ohmic-net/puca_dsp/puca_dsp-platformio-arduino-esp32/original edition/arduino-esp32_stereo_chorus/src/controller_mod.h

/*!
 *  @file       effectmodule.h
 *  Project     Blackstomp Arduino Library
 *  @brief      Blackstomp Library for the Arduino
 *  @author     Hasan Murod
 *  @date       19/11/2020
 *  @license    MIT - Copyright (c) 2020 Hasan Murod
 *
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
 * THE SOFTWARE IS PROVIDED "AS IS", WITHOUT WARRANTY OF ANY KIND, EXPRESS OR
 * IMPLIED, INCLUDING BUT NOT LIMITED TO THE WARRANTIES OF MERCHANTABILITY,
 * FITNESS FOR A PARTICULAR PURPOSE AND NONINFRINGEMENT. IN NO EVENT SHALL THE
 * AUTHORS OR COPYRIGHT HOLDERS BE LIABLE FOR ANY CLAIM, DAMAGES OR OTHER
 * LIABILITY, WHETHER IN AN ACTION OF CONTRACT, TORT OR OTHERWISE, ARISING FROM,
 * OUT OF OR IN CONNECTION WITH THE SOFTWARE OR THE USE OR OTHER DEALINGS IN
 * THE SOFTWARE.
 */
#ifndef CONTROLLERMODULE_H_
#define CONTROLLERMODULE_H_

#include <Arduino.h>

typedef enum
{
  IM_LR,    //input mode = line-in L, line-in R
  IM_LMIC   //input mode = Line-in L, Microphone
} 
INPUT_MODE;

typedef enum
{
  EM_DISABLED,  //Not used
  EM_BUTTONS,   //Push buttons on encoder port
  EM_ROTARY     //Rotary encoder (with push button) on encoder port
} 
ENCODER_MODE;

typedef enum
{
  CM_DISABLED,  //not used
  CM_POT,       //potentiometer
  CM_SELECTOR,  //selector switch
  CM_TOGGLE,    //momentary push button as toggle switch
  CM_MOMENTARY, //momentary push button as momentary switch 
} 
CONTROL_MODE;

typedef enum
{
  BM_DISABLED,
  BM_MOMENTARY,
  BM_TOGGLE,
}
BUTTON_MODE;

struct BUTTON
{
  BUTTON_MODE mode;
  String name;
  bool inverted;
  bool touch;
  int min;
  int max;
  int value;
  int pin;
};

struct CONTROL
{
  String name;
  CONTROL_MODE mode;
  bool inverted;
  int min;
  int max;
  int levelCount;
  int value;
  bool slowSpeed;
  int pin;
};

struct BLETERMINAL
{
	String servUuid;
	String charUuid;
	uint32_t passKey;
};

class controllerModule
{
  public:
  String name;  //the name of your effect pedal
  INPUT_MODE inputMode; 
  ENCODER_MODE encoderMode;
  CONTROL control[6];
  BUTTON button[6];
  BLETERMINAL bleTerminal; 
  unsigned int runningTicks = 0;

  //base class constructor, do basic initialization, don't write a constructor in your descendant class
  controllerModule();
  //base desctructor, do basic deallocation, don't write a desttuctor in your descendant class
  ~controllerModule();

  //you have to write all initialization in the init() function of the  descendant class to set up
  //the name, inMode, and controls, memory allocation, and any other initialization
  virtual void init(){};

  //you have to write all deallocatoin in the deInit() function of the  descendant class for any deallocation
  virtual void deInit(){};

  //you have to overload the following event handler functions in your descendant class when its needed
  virtual void onControlChange(int controlIndex){};
  virtual void onButtonChange(int buttonIndex){};
  virtual void onButtonPress(int buttonIndex){};
  virtual void onButtonRelease(int buttonIndex){};
  virtual void onBleTerminalRequest(const char* request, char* response){};

};

#endif
