ohmic-net/puca_dsp/puca_dsp-platformio-arduino-esp32/original edition/arduino-esp32_stereo_chorus/src/bsdsp.cpp

/*!
 *  @file       bsdsp.cpp
 *  Project     Blackstomp Arduino Library
 *  @brief      Blackstomp Library for the Arduino
 *  @author     Hasan Murod
 *  @date       19/11/2020
 *  @license    MIT - Copyright (c) 2020 Hasan Murod
 *
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
 * THE SOFTWARE IS PROVIDED "AS IS", WITHOUT WARRANTY OF ANY KIND, EXPRESS OR
 * IMPLIED, INCLUDING BUT NOT LIMITED TO THE WARRANTIES OF MERCHANTABILITY,
 * FITNESS FOR A PARTICULAR PURPOSE AND NONINFRINGEMENT. IN NO EVENT SHALL THE
 * AUTHORS OR COPYRIGHT HOLDERS BE LIABLE FOR ANY CLAIM, DAMAGES OR OTHER
 * LIABILITY, WHETHER IN AN ACTION OF CONTRACT, TORT OR OTHERWISE, ARISING FROM,
 * OUT OF OR IN CONNECTION WITH THE SOFTWARE OR THE USE OR OTHER DEALINGS IN
 * THE SOFTWARE.
 */
  
#include "bsdsp.h"
#include "task.h"
#include <math.h>

//######################################################################
// LOOKUPLINEAR
float lookupLinear(float x, const float* table)
{
  int index = (int)x;
  float frac = x - (float)index;
  return table[index] + frac * (table[index+1]-table[index]);
}

//######################################################################
// SINE OSCILLATOR
#define MAXPHASE 255.0
oscillator::oscillator()
{
	phase = 0;
	phaseincrement = 0;
	setFrequency(20);
	waveTable = sin_table;
}

void oscillator::setWaveTable(const float* wtable)
{
	if(wtable==NULL)
		waveTable = sin_table;
	else waveTable = wtable;
}

void oscillator::update()
{
  phase = phase + phaseincrement;
  if(phase > MAXPHASE)
    phase = phase-MAXPHASE;
}

void oscillator::setPhase(float p)
{
	phase = p;
}

void oscillator::setFrequency(float freq)
{
  phaseincrement = freq * MAXPHASE /(float)SAMPLE_RATE;
}

float oscillator::getOutput(float phaseOffset)
{
  float p = phase + phaseOffset;
  if(p>MAXPHASE)
    p = p - MAXPHASE;
  return lookupLinear(p,waveTable);
}

float oscillator::getOutput()
{
  return lookupLinear(phase,waveTable);
}

//######################################################################
// BIQUAD FILTER
// Implementation of direct-form-2 biquad iir filter

//direct-form-2 biquad iir filter
struct biquadState
{
  float coef[5]; //a1, a2, b0, b1, b2
  float w[2];
};

biquadFilter::biquadFilter(int stageCount)
{
  stages = stageCount;
  biquadState* s = new biquadState[stages];
  states = (void*) s;
  for(int i=0;i<stages;i++)
  {
    s[i].w[0]=0;
    s[i].w[1]=0;
  }
}

/*
biquadFilter::~biquadFilter()
{
  biquadState* sp = (biquadState*) states;
  delete[] states;
}
*/

void biquadFilter::setCoef(const float* coef)
{
  biquadState* sp = (biquadState*) states;
  for(int i=0;i<stages;i++)
  {
    for(int n=0;n<5;n++)
      sp[i].coef[n]=coef[(5*i)+n];
  }
}

void biquadFilter::reset()
{
	biquadState* sp = (biquadState*) states;
    for(int i=0;i<stages;i++)
    {
      sp[i].w[0]=0;
      sp[i].w[1]=0;
    }
}

void biquadFilter::process(const float* in, float* out, int sampleCount)
{
  biquadState* sp = (biquadState*) states;
  for(int i=0;i<sampleCount;i++)
  {
    float input = in[i];
    for(int s=0; s<stages; s++) 
    {
      float temp = input + sp[s].coef[3] * sp[s].w[0] + sp[s].coef[4]*sp[s].w[1];
      input = temp * sp[s].coef[0] + sp[s].coef[1] * sp[s].w[0] + sp[s].coef[2]*sp[s].w[1];
      sp[s].w[1]=sp[s].w[0];
      sp[s].w[0]=temp;
    }
    out[i]=input;
  }
}

float biquadFilter::process(float in)
{
	biquadState* sp = (biquadState*) states;
	float input = in;
    for(int s=0; s<stages; s++) 
    {
      float temp = input + sp[s].coef[3] * sp[s].w[0] + sp[s].coef[4]*sp[s].w[1];
      input = temp * sp[s].coef[0] + sp[s].coef[1] * sp[s].w[0] + sp[s].coef[2]*sp[s].w[1];
      sp[s].w[1]=sp[s].w[0];
      sp[s].w[0]=temp;
    }
    return input;
}

//######################################################################
// FRACTIONAL DELAY
fractionalDelay::fractionalDelay()
{
	bufflength=0;
	writeIndex=0;
	buffer = NULL;
}

bool fractionalDelay::init(float maxDelayInMs)
{
	if(buffer!=NULL)
		return false;
		
	maxdelay = maxDelayInMs;
	sampleCountPerMs = SAMPLE_RATE/1000;
	bufflength = ceilf(maxDelayInMs * sampleCountPerMs)+1;
	buffer = new float[bufflength];

	if(buffer!=NULL)
	{
		for(int i=0;i<bufflength;i++)
			buffer[i]=0;
		return true;
	}
	else return false;
}

fractionalDelay::~fractionalDelay()
{
	if(buffer != NULL)
		delete[] buffer;
}

void fractionalDelay::write(float sample)
{
	writeIndex++;
	if(writeIndex>=bufflength)
		writeIndex=0;
	buffer[writeIndex]=sample;
}

float fractionalDelay::read(float delayInMs)
{
	float indexpos = (float)writeIndex - (sampleCountPerMs * delayInMs);
	if(indexpos < 0)
		indexpos = (float)bufflength + indexpos;
		
	int index0= (int) indexpos;
	float frac = indexpos - (float) index0;
	int index1 = index0 + 1;
	if(index1==bufflength)
		index1=0;
	//linear interpolate at fractional point
	return buffer[index0] + frac * (buffer[index1]-buffer[index0]);
}

//######################################################################
// WAVESHAPER
waveShaper::waveShaper()
{
	//initialize the transfer function table with default function
	for(int i=0;i<256;i++)
	{
		float x = ((float)i-127.5f)/127.5f;
		transferFunctionTable[i]=2.0f/(1+expf(-6.0f*x))-1.0f;
	}
}

float waveShaper::process(float in)
{
	float val = (in+1.0f)*127.5f;
	if(val<0.0f) val = 0.0f;
	if(val>255.0f) val=255.0f;
	return lookupLinear(val,transferFunctionTable);
}

void waveShaper::process(float* in, float* out, int sampleCount)
{
	for(int i=0;i<sampleCount;i++)
	{
		float val = (in[i]+1.0f)*127.5f;
		if(val<0.0f) val = 0.0f;
		if(val>255.0f) val=255.0f;
		out[i]= lookupLinear(val,transferFunctionTable);
	}
}

//######################################################################
// RC HIGH-PASS FILTER
rcHiPass::rcHiPass()
{
	vc=0;
	setCutOff(20);
}

void rcHiPass::setTimeConstant(float val)
{
	tc = val;
}

void rcHiPass::setCutOff(float val)
{
	tc = 1/(6.283*val);
}

float rcHiPass::process(float in)
{
	float delta = (in-vc)/(tc*44100);
	vc = vc + delta;
	return in-vc;
}

void rcHiPass::process(float* in, float* out, int sampleCount)
{
	for(int i=0;i<sampleCount;i++)
	{
		float delta = (in[i]-vc)/(tc*44100);
		vc = vc + delta;
		out[i]=in[i]-vc;
	}
}

//######################################################################
// RC LOW-PASS FILTER
rcLoPass::rcLoPass()
{
	vc=0;
	setCutOff(1000);
}

void rcLoPass::setTimeConstant(float val)
{
	tc = val;
}

void rcLoPass::setCutOff(float val)
{
	tc = 1/(6.283*val);
}

float rcLoPass::process(float in)
{
	float delta = (in-vc)/(tc*44100);
	vc = vc + delta;
	return vc;
}

void rcLoPass::process(float* in, float* out, int sampleCount)
{
	for(int i=0;i<sampleCount;i++)
	{
		float delta = (in[i]-vc)/(tc*44100);
		vc = vc + delta;
		out[i]=vc;
	}
}

//######################################################################
// SIMPLE TONE
simpleTone::simpleTone()
{
	hiPass.setTimeConstant(0.0001078); //emulate big muff R22k and C4.9nF
	loPass.setTimeConstant(0.00039); //emulate big muff R39k and C10nF
}

void simpleTone::setTone(float val)
{
	tone = val;
}

float simpleTone::process(float in)
{
	return tone * hiPass.process(in) + (1-tone) * loPass.process(in);
}

void simpleTone::process(float* in, float* out, int sampleCount)
{
	for(int i=0;i<sampleCount;i++)
	{
		out[i] = tone * hiPass.process(in[i]) + (1-tone) * loPass.process(in[i]);
	}
}

//######################################################################
// NOISE GATE

noiseGate::noiseGate()
{
	envelope = 0;
	setThreshold(0);
	
	//2 stages = 4th order
	lpf = new biquadFilter(2);
	
	//4th order 20Hz lpf (44.1KHz)
	const float co[] = 
	{
		0.000002152381733479521, 0.000004304763466959042, 0.000002152381733479521, 1.9947405124091158, -0.9947486108316238,// b0, b1, b2, a1, a2
		0.0000019073486328125, 0.000003814697265625, 0.0000019073486328125, 1.997813341671618, -0.9978214525694677// b0, b1, b2, a1, a2
	};
	lpf->setCoef(co);
}

float noiseGate::process(float in)
{
	envelope = 1.4142 * lpf->process(fabsf(in));
	
	//detecting the gate and expansion area
	if(envelope < lowerTh)
	{
		in = 0;
	}
	else if(envelope < upperTh)
	{
		in = in * (envelope - lowerTh)/(upperTh-lowerTh);
	}
	return in;
}

void noiseGate::process(float* in, float* out, int sampleCount)
{
	for(int i=0;i<sampleCount;i++)
	{
		out[i]=process(in[i]);
	}
}

//0 = -70dB, 1 = -10dB
void noiseGate::setThreshold(float val)
{
	float dB = -70.0f + 60.0f * val;
	upperTh = powf(10,dB/20.0f);
	lowerTh = upperTh/2.0f;
}
