ohmic-net/puca_dsp/puca_dsp-platformio-arduino-esp32/original edition/arduino-esp32_stereo_chorus/src/dsptable.h

#ifndef DSPTABLE_H_
#define DSPTABLE_H_

const float sin_table[] =  //256 samples, full wave +1 to -1
{
  0.00000000  ,
  0.02463745  ,
  0.04925994  ,
  0.07385253  ,
  0.09840028  ,
  0.12288829  ,
  0.14730170  ,
  0.17162568  ,
  0.19584547  ,
  0.21994636  ,
  0.24391372  ,
  0.26773300  ,
  0.29138975  ,
  0.31486959  ,
  0.33815827  ,
  0.36124167  ,
  0.38410575  ,
  0.40673664  ,
  0.42912061  ,
  0.45124406  ,
  0.47309356  ,
  0.49465584  ,
  0.51591783  ,
  0.53686660  ,
  0.55748944  ,
  0.57777383  ,
  0.59770746  ,
  0.61727822  ,
  0.63647424  ,
  0.65528385  ,
  0.67369564  ,
  0.69169844  ,
  0.70928131  ,
  0.72643357  ,
  0.74314483  ,
  0.75940492  ,
  0.77520398  ,
  0.79053241  ,
  0.80538092  ,
  0.81974048  ,
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
};

const float hann_table[] =
{
	0.00000000	,
	0.00015177	,
	0.00060700	,
	0.00136541	,
	0.00242654	,
	0.00378975	,
	0.00545420	,
	0.00741888	,
	0.00968261	,
	0.01224402	,
	0.01510153	,
	0.01825343	,
	0.02169779	,
	0.02543253	,
	0.02945537	,
	0.03376389	,
	0.03835545	,
	0.04322727	,
	0.04837640	,
	0.05379971	,
	0.05949390	,
	0.06545553	,
	0.07168096	,
	0.07816643	,
	0.08490798	,
	0.09190154	,
	0.09914286	,
	0.10662753	,
	0.11435102	,
	0.12230863	,
	0.13049554	,
	0.13890677	,
	0.14753723	,
	0.15638166	,
	0.16543470	,
	0.17469085	,
	0.18414450	,
	0.19378990	,
	0.20362120	,
	0.21363243	,
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
};

#endif
