ohmic-net/puca_dsp/puca_dsp-platformio-arduino-esp32/original edition/arduino-esp32_stereo_chorus/src/set_codec.h

#ifndef ESCODEC_H_
#define ESCODEC_H_

 #include "codec.h"

//~~~~~~~~~~~~~~~~~~~~~~~~~~~~~~~~~~~~~~~~~~~~~~~~~~~~~~~
//declaration of codec, an instance of Codec with extern
            extern Codec codec;
//~~~~~~~~~~~~~~~~~~~~~~~~~~~~~~~~~~~~~~~~~~~~~~~~~~~~~~~

void codec_sets();

#endif
