ohmic-net/puca_dsp/puca_dsp-platformio-arduino-esp32/original edition/arduino-esp32_fft_example/include/arduinoFFT.h

/*

	FFT libray
	Copyright (C) 2010 Didier Longueville
	Copyright (C) 2014 Enrique Condes

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
*/

#ifndef arduinoFFT_h /* Prevent loading library twice */
#define arduinoFFT_h
#ifdef ARDUINO
	#if ARDUINO >= 100
		#include "Arduino.h"
	#else
		#include "WProgram.h" /* This is where the standard Arduino code lies */
	#endif
#else
	#include <stdlib.h>
	#include <stdio.h>
	#ifdef __AVR__
		#include <avr/io.h>
	#endif
	#include <math.h>
	#include "defs.h"
	#include "types.h"
#endif

#define FFT_LIB_REV 0x14
/* Custom constants */
#define FFT_FORWARD 0x01
#define FFT_REVERSE 0x00

/* Windowing type */
#define FFT_WIN_TYP_RECTANGLE 0x00 /* rectangle (Box car) */
#define FFT_WIN_TYP_HAMMING 0x01 /* hamming */
#define FFT_WIN_TYP_HANN 0x02 /* hann */
#define FFT_WIN_TYP_TRIANGLE 0x03 /* triangle (Bartlett) */
#define FFT_WIN_TYP_NUTTALL 0x04 /* nuttall */
#define FFT_WIN_TYP_BLACKMAN 0x05 /* blackman */
#define FFT_WIN_TYP_BLACKMAN_NUTTALL 0x06 /* blackman nuttall */
#define FFT_WIN_TYP_BLACKMAN_HARRIS 0x07 /* blackman harris*/
#define FFT_WIN_TYP_FLT_TOP 0x08 /* flat top */
#define FFT_WIN_TYP_WELCH 0x09 /* welch */
/*Mathematial constants*/
#define twoPi 6.28318531
#define fourPi 12.56637061
#define sixPi 18.84955593

class arduinoFFT {
public:
	/* Constructor */
//	arduinoFFT(void);
	arduinoFFT(float *vReal, float *vImag, uint16_t samples, float samplingFrequency);
	/* Destructor */
	~arduinoFFT(void);
	/* Functions */
	uint8_t Revision(void);
	uint8_t Exponent(uint16_t value);
//	void ComplexToMagnitude(float *vReal, float *vImag, uint16_t samples);
//	void Compute(float *vReal, float *vImag, uint16_t samples, uint8_t dir);
//	void Compute(float *vReal, float *vImag, uint16_t samples, uint8_t power, uint8_t dir);
//	void DCRemoval(float *vData, uint16_t samples);
//	float MajorPeak(float *vD, uint16_t samples, float samplingFrequency);
//	void Windowing(float *vData, uint16_t samples, uint8_t windowType, uint8_t dir);
	void ComplexToMagnitude();
	void Compute(uint8_t dir);
	void DCRemoval();
	float MajorPeak();
	void Windowing(uint8_t windowType, uint8_t dir);

	void MajorPeak(float *f, float *v);
//	void MajorPeak(float *vD, uint16_t samples, float samplingFrequency, float *f, float *v);


private:
	/* Variables */
	uint16_t _samples;
	float _samplingFrequency;
	float *_vReal;
	float *_vImag;
	uint8_t _power;
	/* Functions */
	void Swap(float *x, float *y);
};

#endif
